VanPeltT/Harmonic-Mount-and-Controller/Electronics/StepperDrivers.png

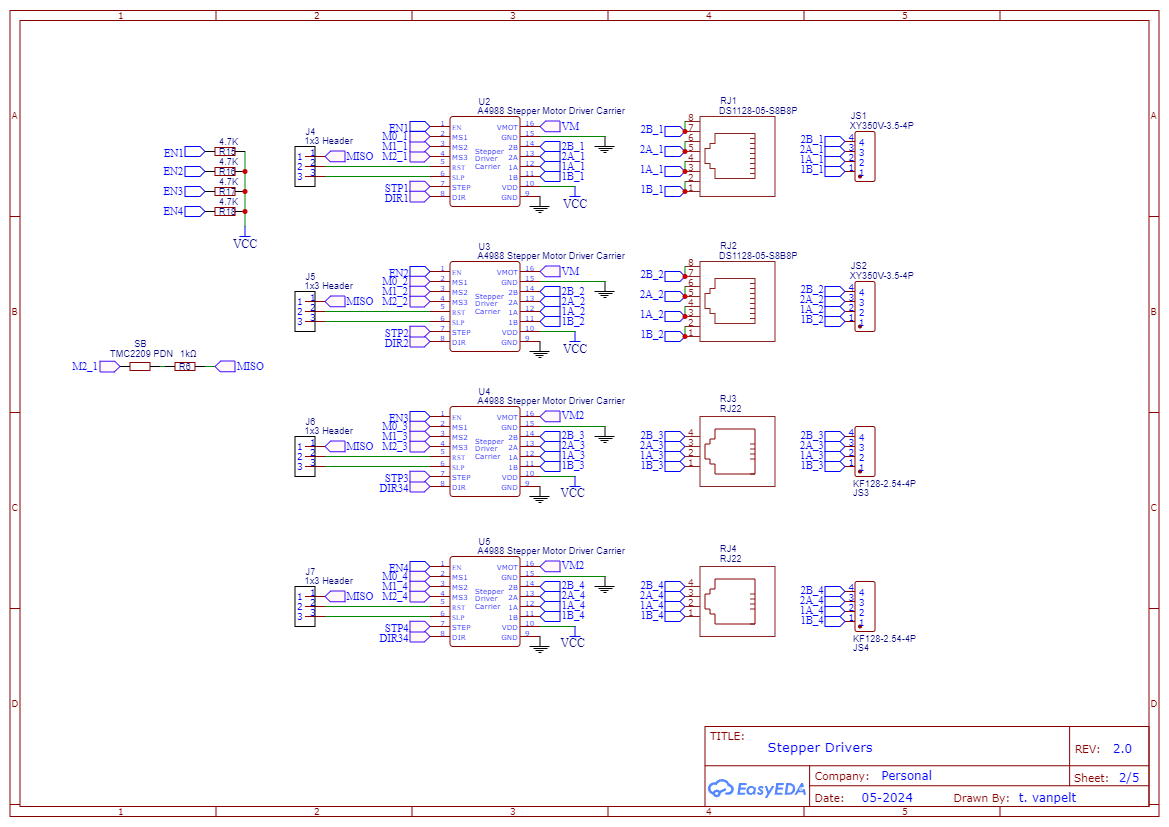
Electronics/StepperDrivers.png
