VanPeltT/Harmonic-Mount-and-Controller/Electronics/Teensy.png

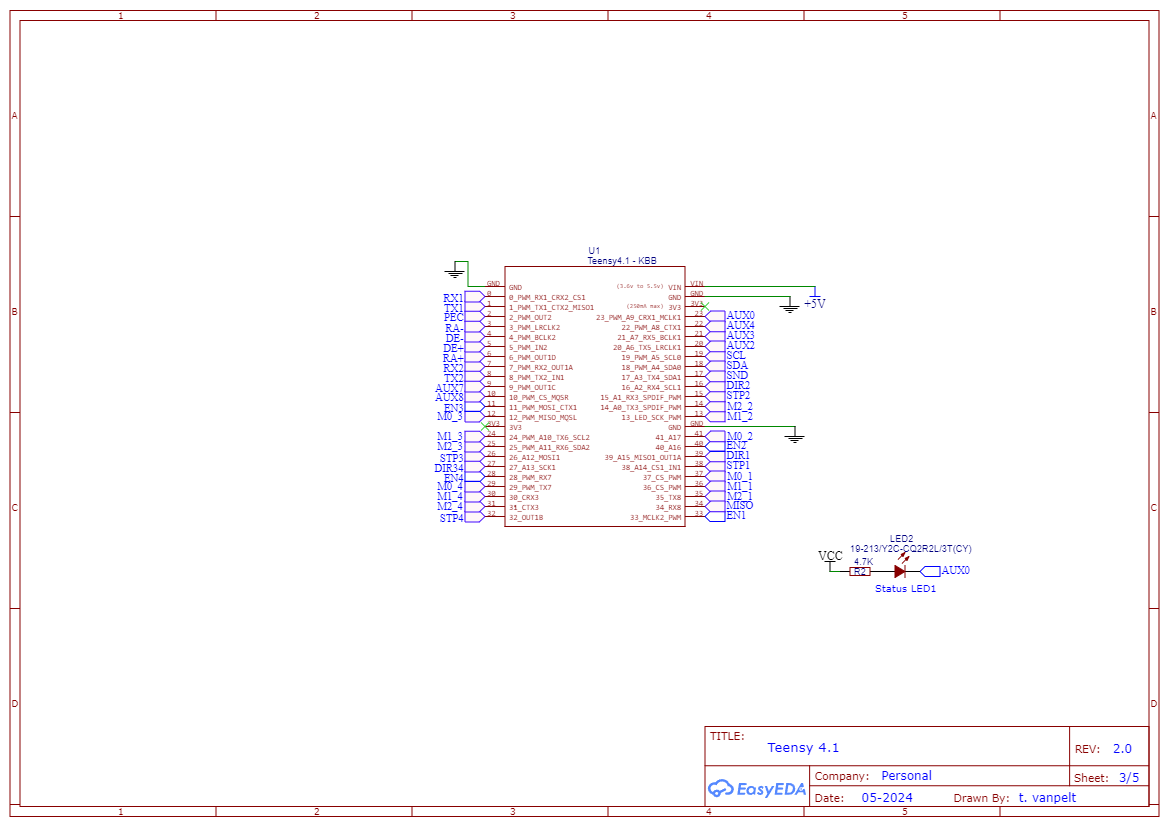
Electronics/Teensy.png
