VanPeltT/Harmonic-Mount-and-Controller/Pictures/20240726_051934.jpg

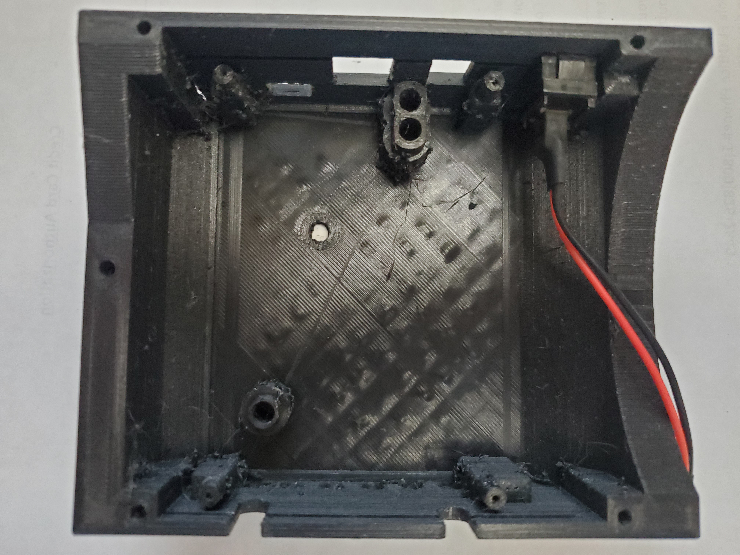
Pictures/20240726_051934.jpg
