VanPeltT/Harmonic-Mount-and-Controller/Pictures/20240726_051948.jpg

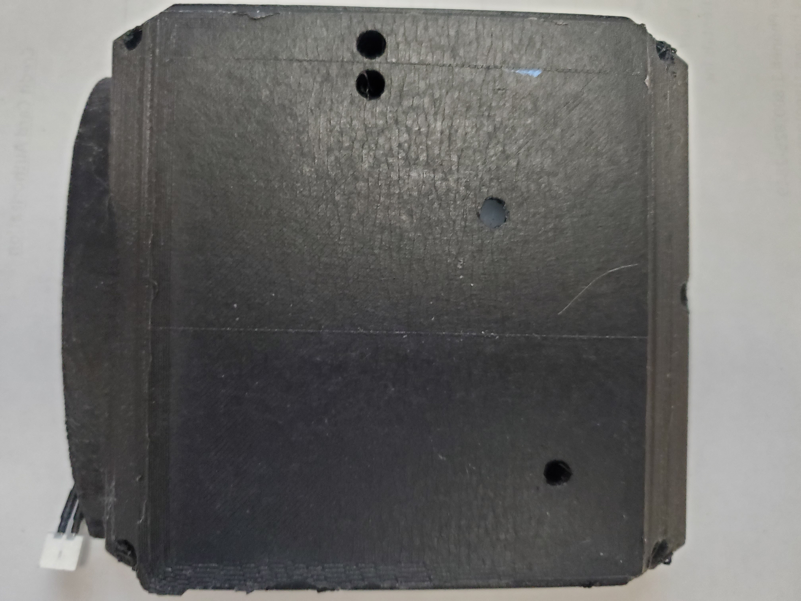
Pictures/20240726_051948.jpg
