VanPeltT/Harmonic-Mount-and-Controller/Pictures/20240726_053850.jpg

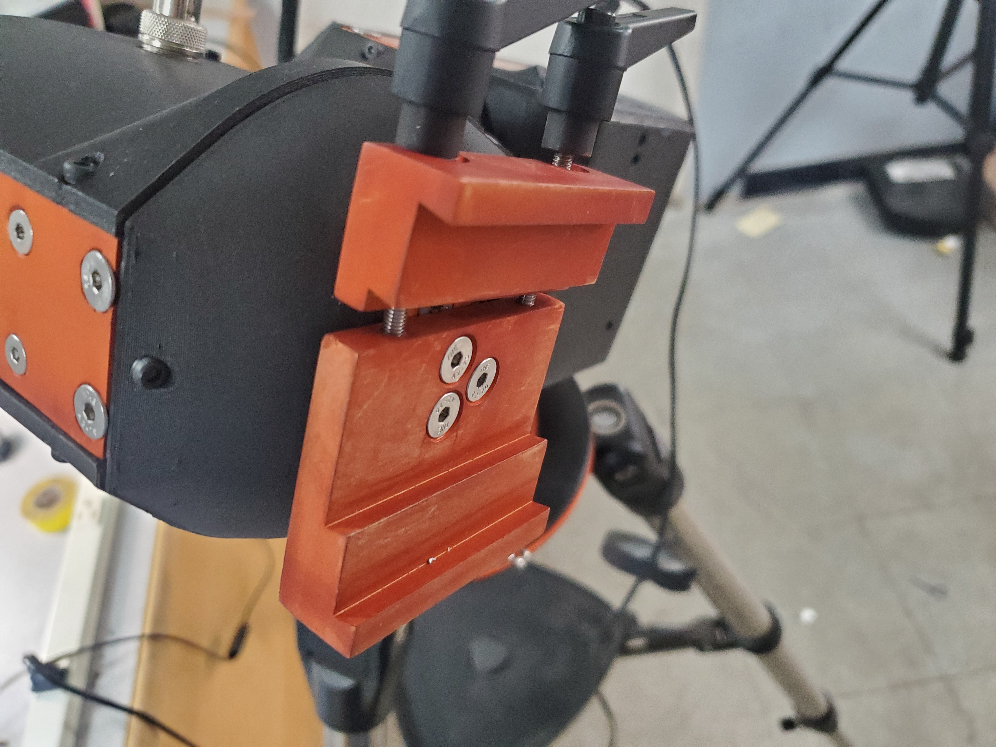
Pictures/20240726_053850.jpg
