VanPeltT/Harmonic-Mount-and-Controller/Pictures/20240726_053929.jpg

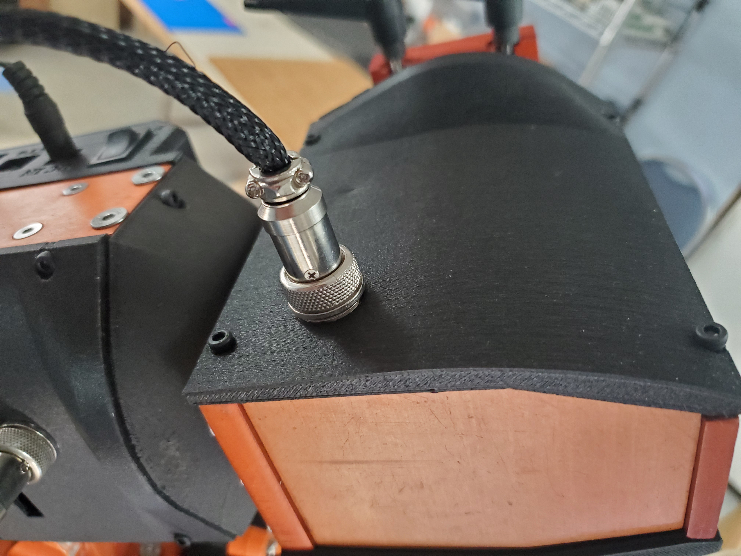
Pictures/20240726_053929.jpg
