VanPeltT/Harmonic-Mount-and-Controller/Pictures/20240726_054036.jpg

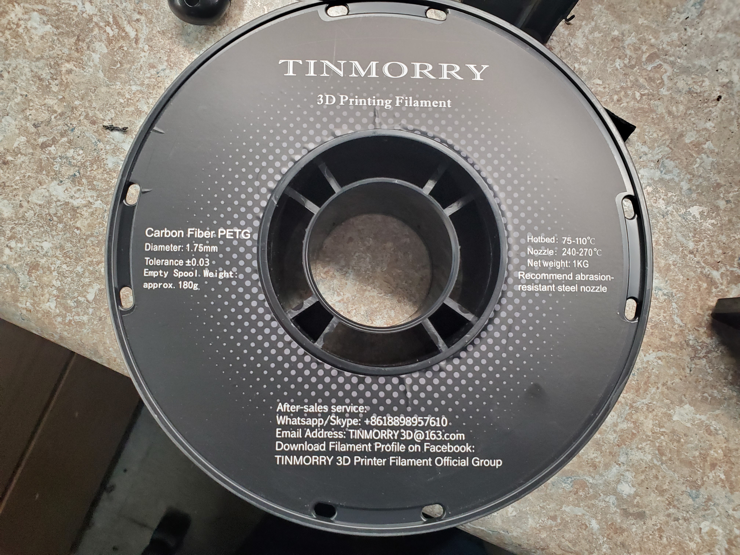
Pictures/20240726_054036.jpg
