VanPeltT/Harmonic-Mount-and-Controller/Pictures/20240726_054247.jpg

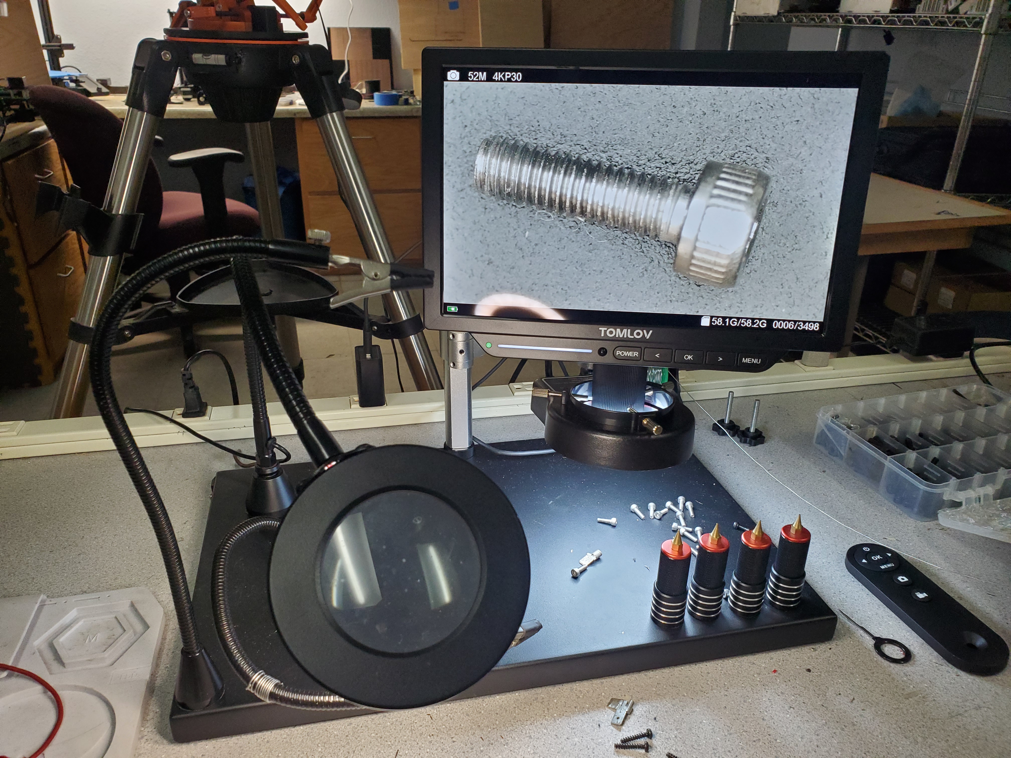
Pictures/20240726_054247.jpg
