VanPeltT/Harmonic-Mount-and-Controller/Pictures/20240726_055059.jpg

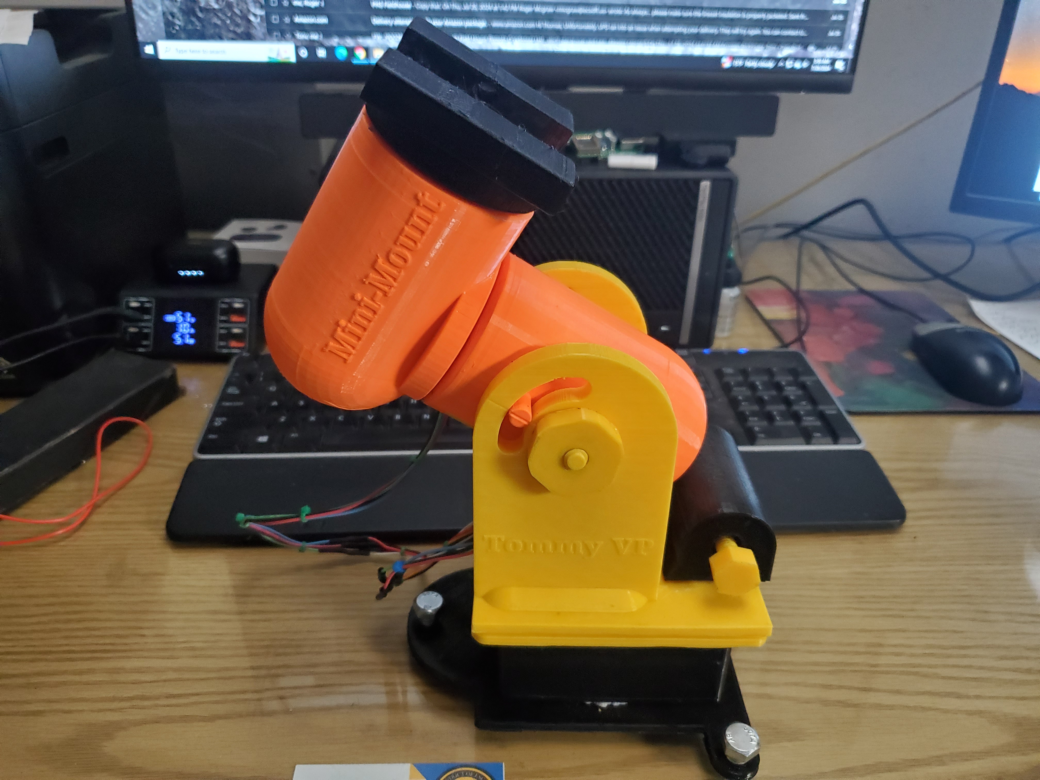
Pictures/20240726_055059.jpg
