VanPeltT/Harmonic-Mount-and-Controller/Pictures/20240726_055125.jpg

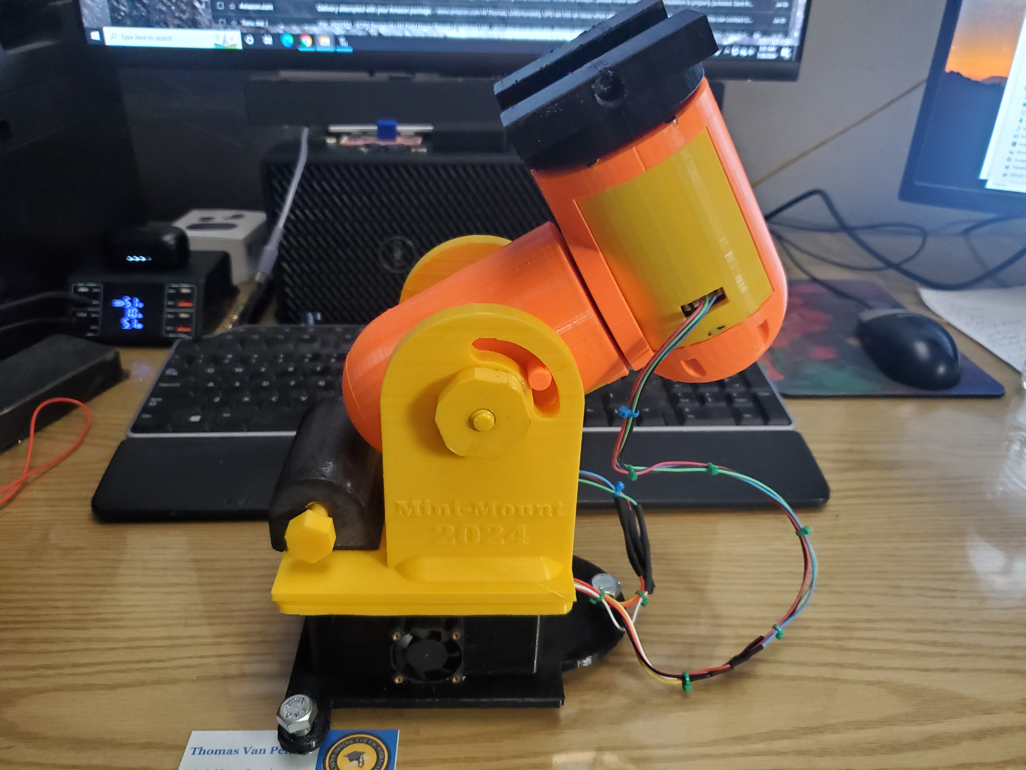
Pictures/20240726_055125.jpg
