VanPeltT/Harmonic-Mount-and-Controller/Bonus And Future/Pi Step Catalog.png

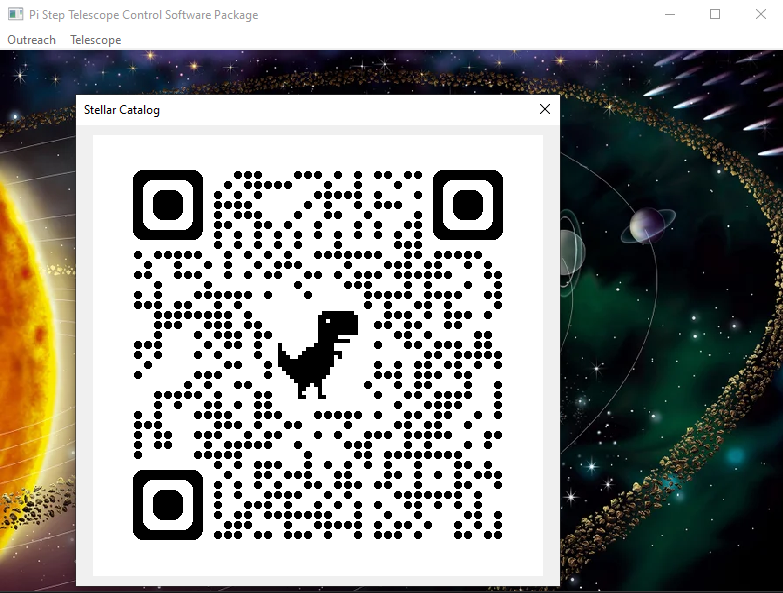
Bonus And Future/Pi Step Catalog.png
