VanPeltT/Harmonic-Mount-and-Controller/Bonus And Future/Pi Step EAAA.png

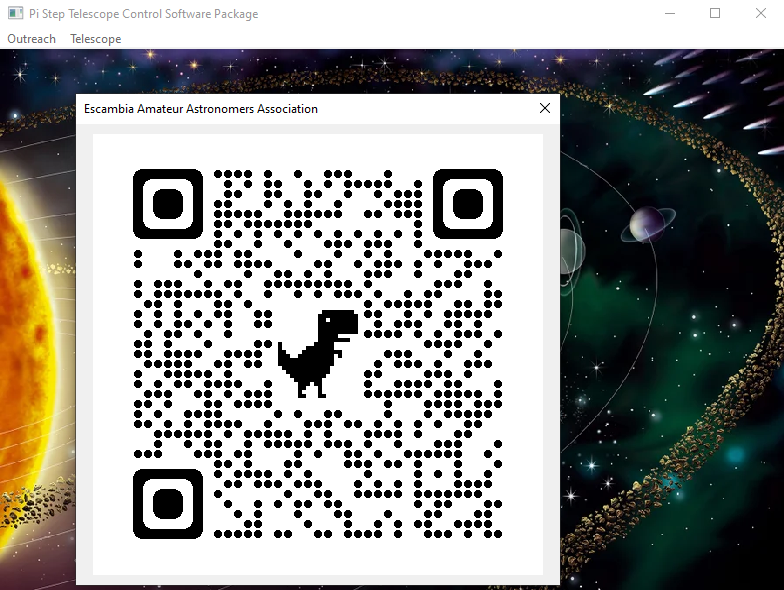
Bonus And Future/Pi Step EAAA.png
