VanPeltT/Harmonic-Mount-and-Controller/Bonus And Future/Pi Step.bmp

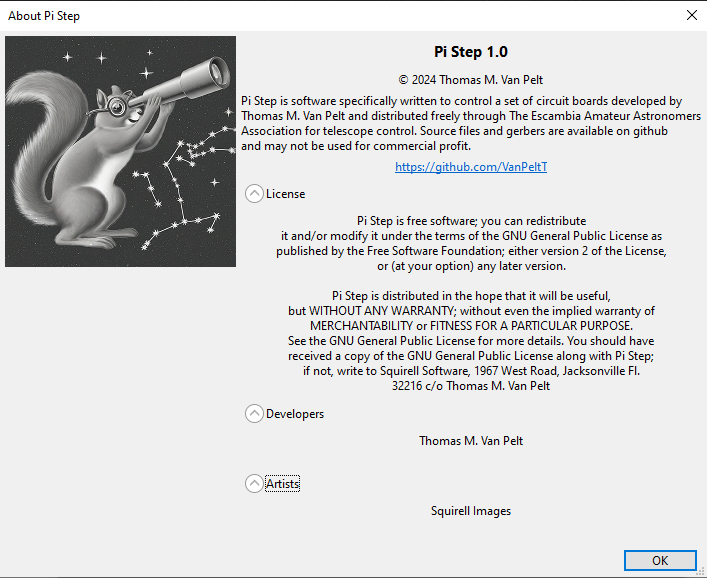
Bonus And Future/Pi Step.bmp
