VanPeltT/Harmonic-Mount-and-Controller/Bonus And Future/Pi Step.png

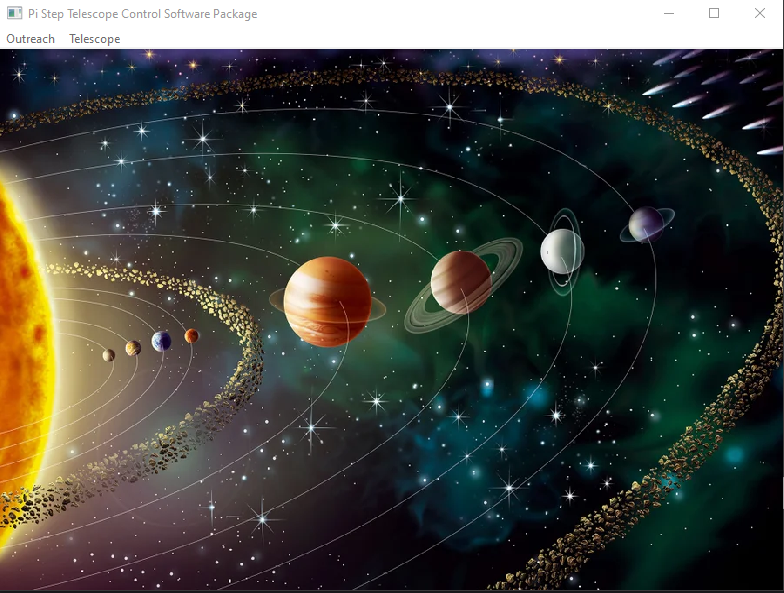
Bonus And Future/Pi Step.png
